VCHSRobots/TalonBreakoutV2/doc/IMG_9758.jpg

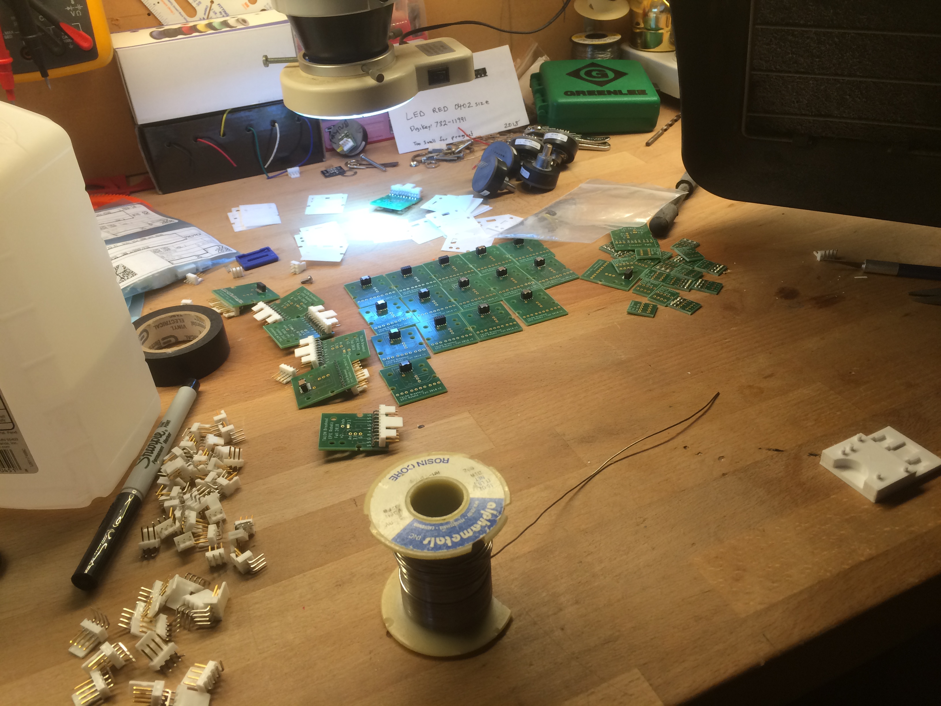
doc/IMG_9758.jpg
