VCHSRobots/TalonBreakoutV2/doc/IMG_9759.jpg

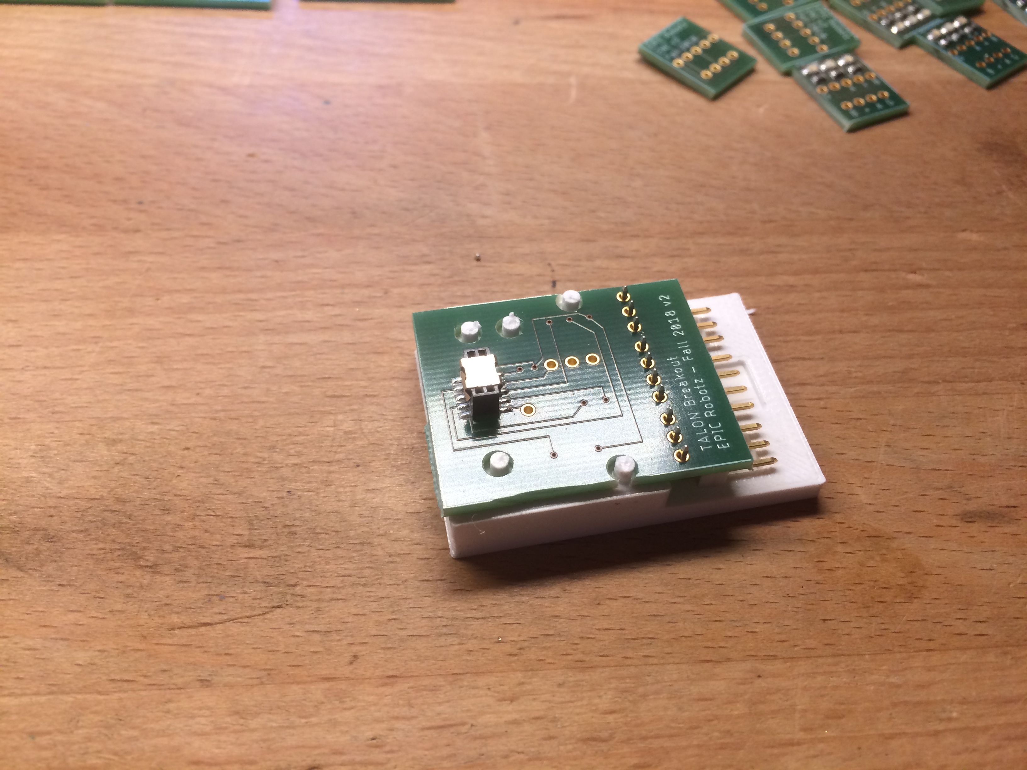
doc/IMG_9759.jpg
