VCHSRobots/TalonBreakoutV2/doc/IMG_9760.jpg

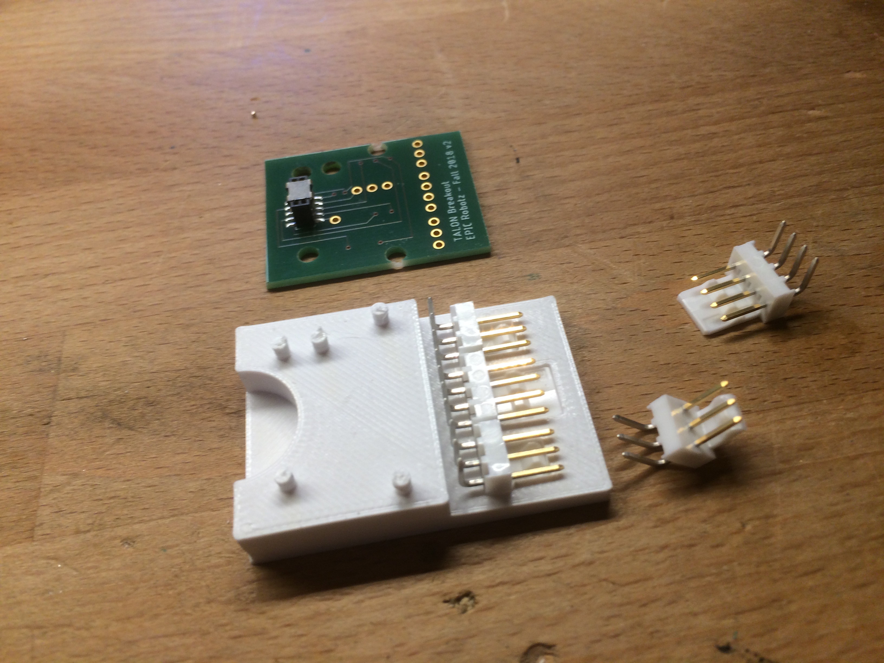
doc/IMG_9760.jpg
