VCHSRobots/TalonBreakoutV2/doc/IMG_9761.jpg

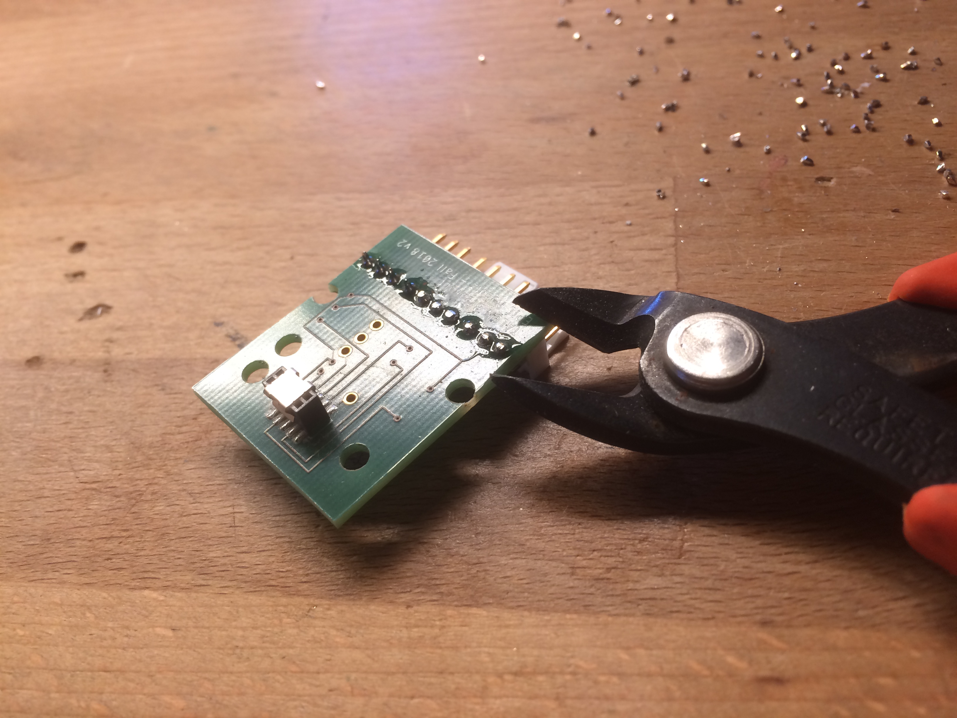
doc/IMG_9761.jpg
