VCHSRobots/TalonBreakoutV2/doc/IMG_9762.jpg

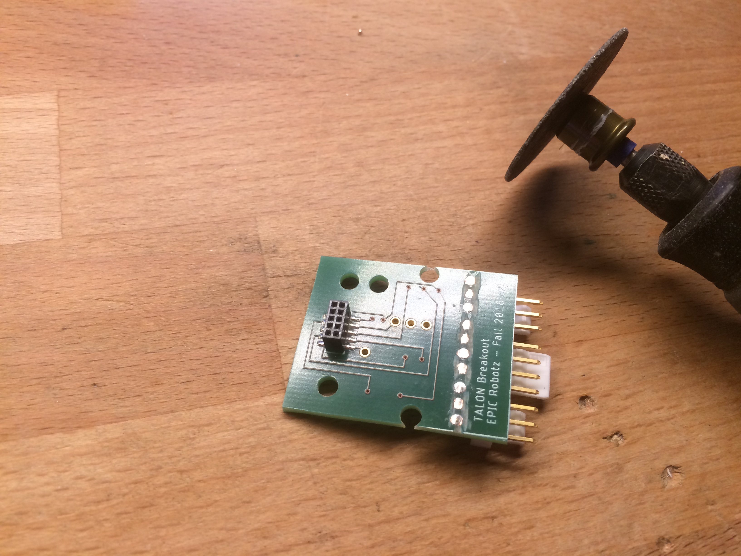
doc/IMG_9762.jpg
