VCHSRobots/TalonBreakoutV2/doc/IMG_9763.jpg

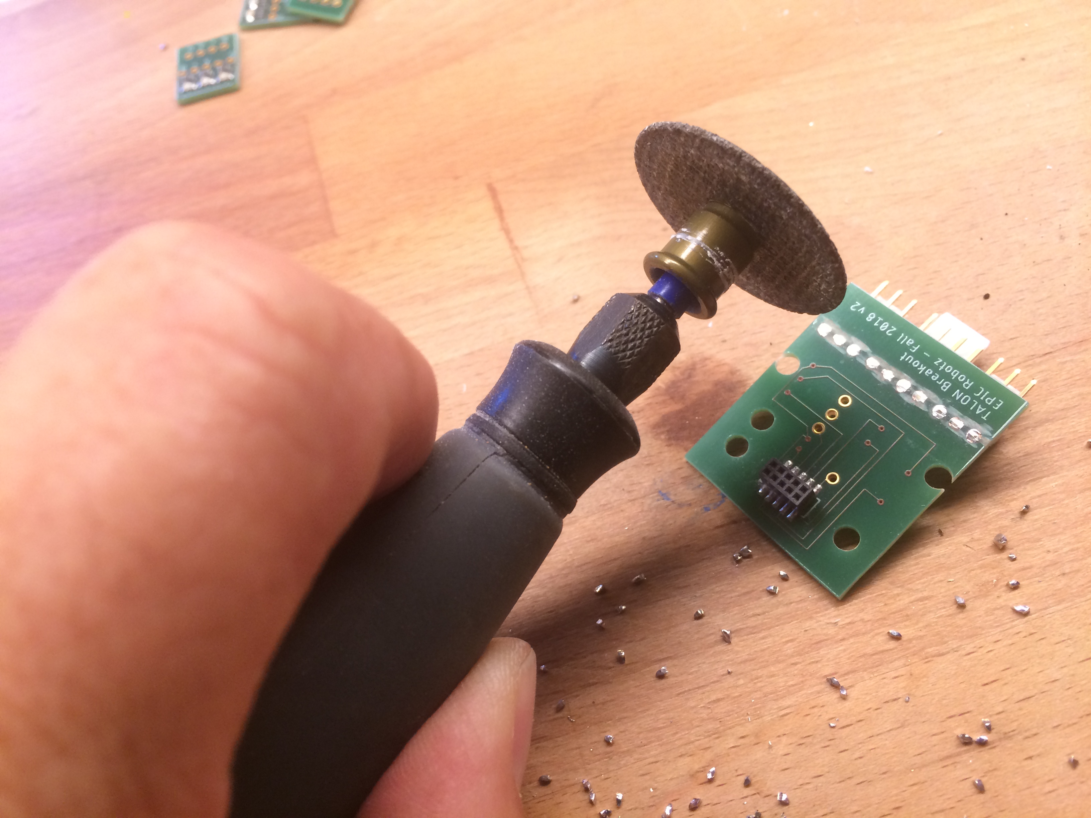
doc/IMG_9763.jpg
