VCHSRobots/TalonBreakoutV2/doc/IMG_9764.jpg

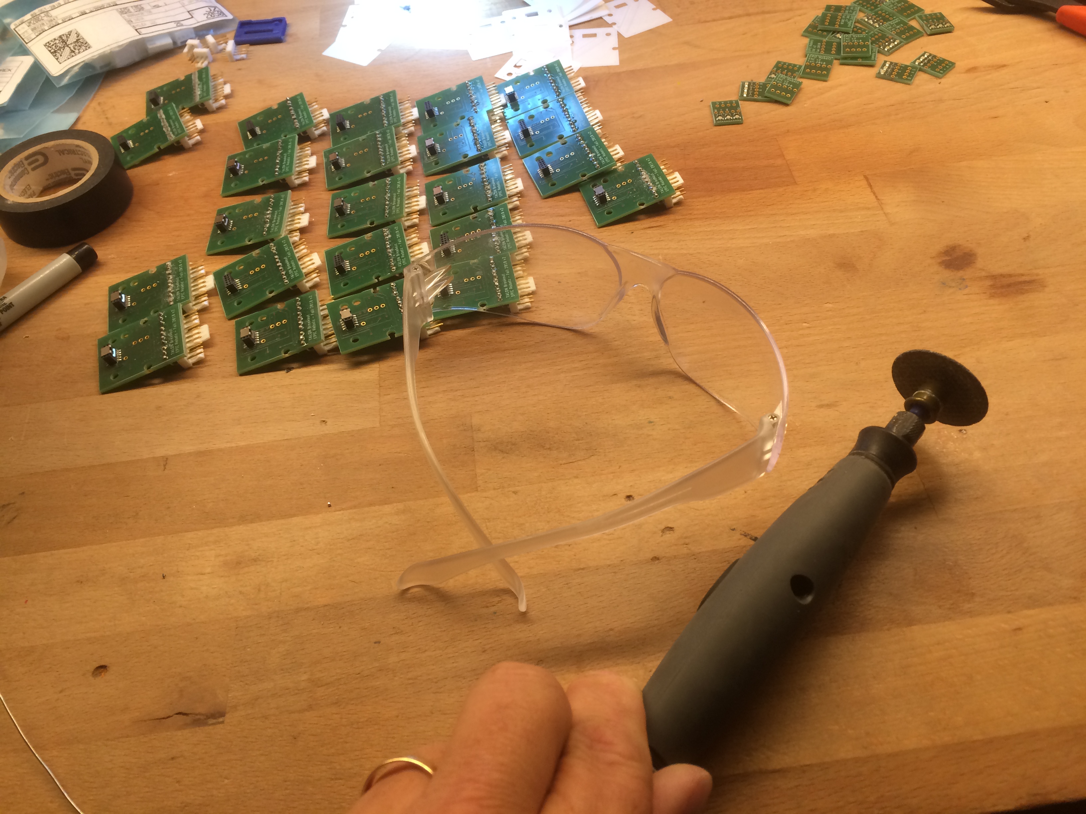
doc/IMG_9764.jpg
