VCHSRobots/TalonBreakoutV2/doc/IMG_9765.jpg

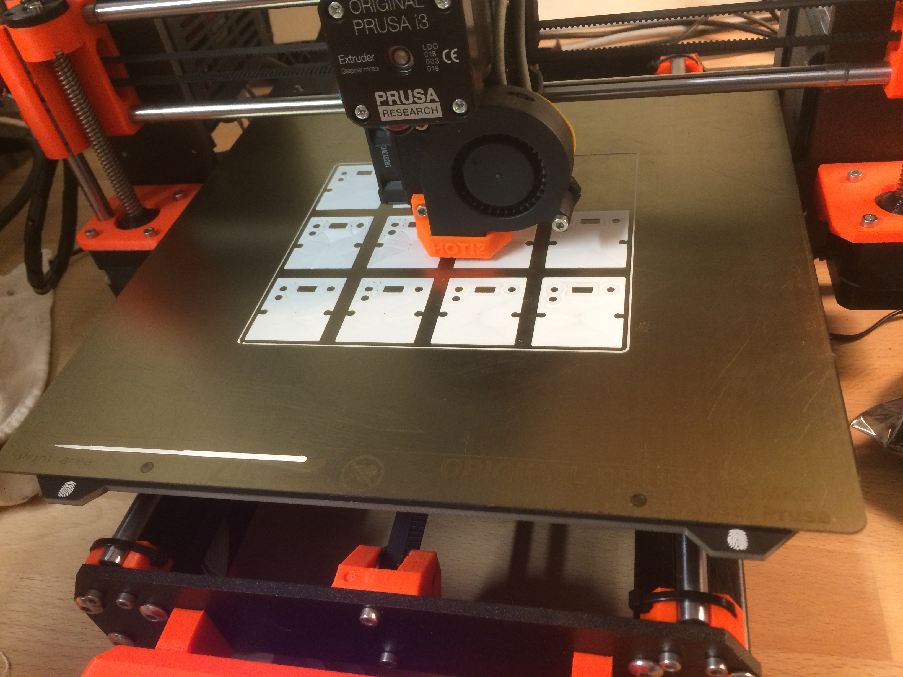
doc/IMG_9765.jpg
