VCHSRobots/TalonBreakoutV2/doc/IMG_9766.jpg

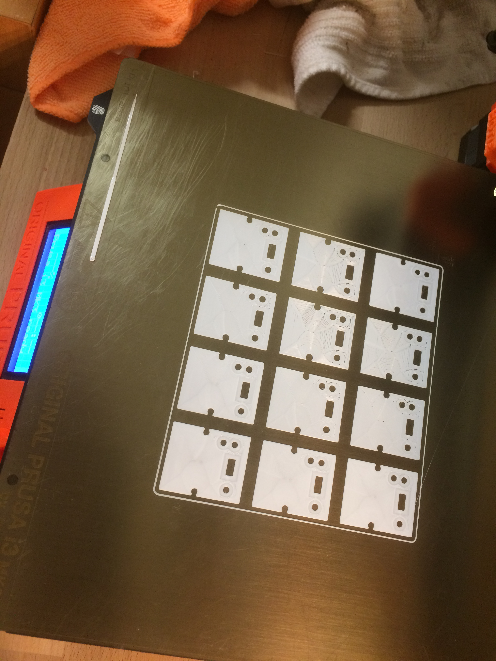
doc/IMG_9766.jpg
