VCHSRobots/TalonBreakoutV2/doc/IMG_9767.jpg

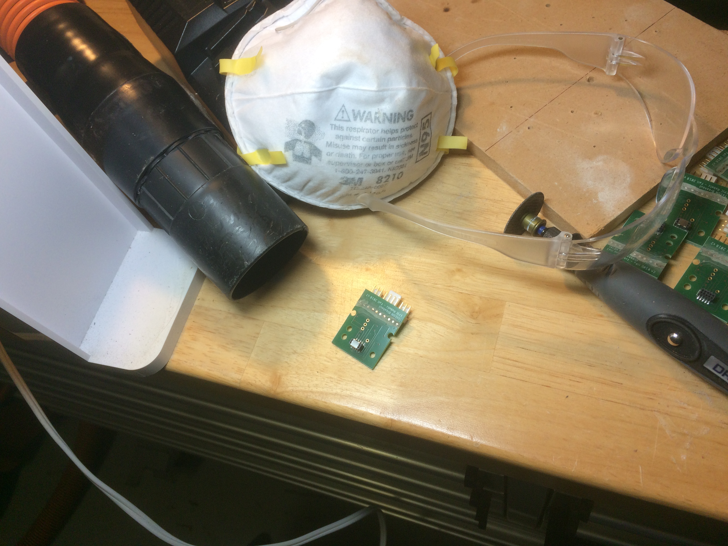
doc/IMG_9767.jpg
