VCHSRobots/TalonBreakoutV2/doc/IMG_9768.jpg

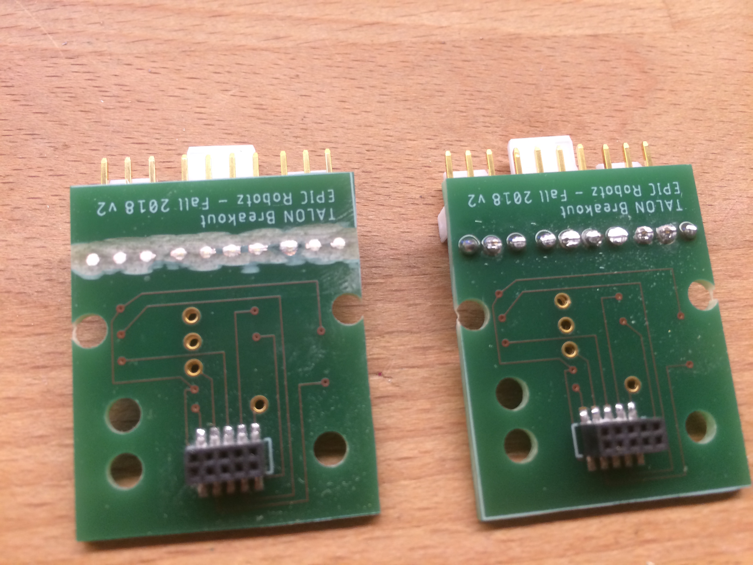
doc/IMG_9768.jpg
