VCHSRobots/TalonBreakoutV2/doc/IMG_9769.jpg

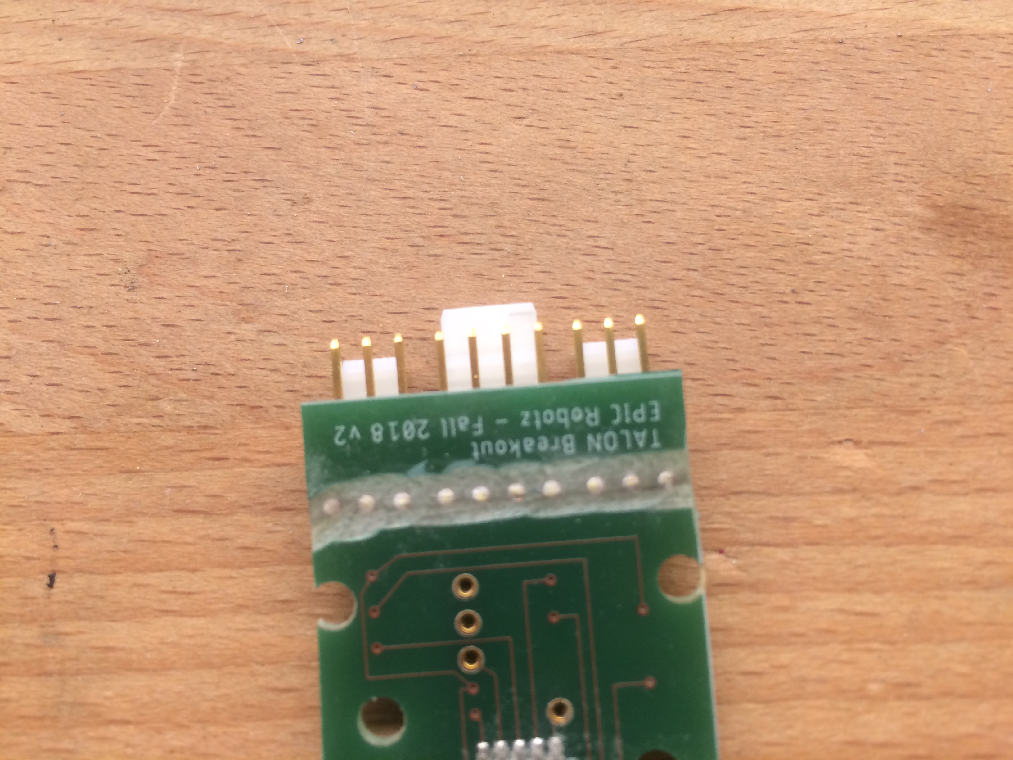
doc/IMG_9769.jpg
