VCHSRobots/TalonBreakoutV2/doc/IMG_9770.jpg

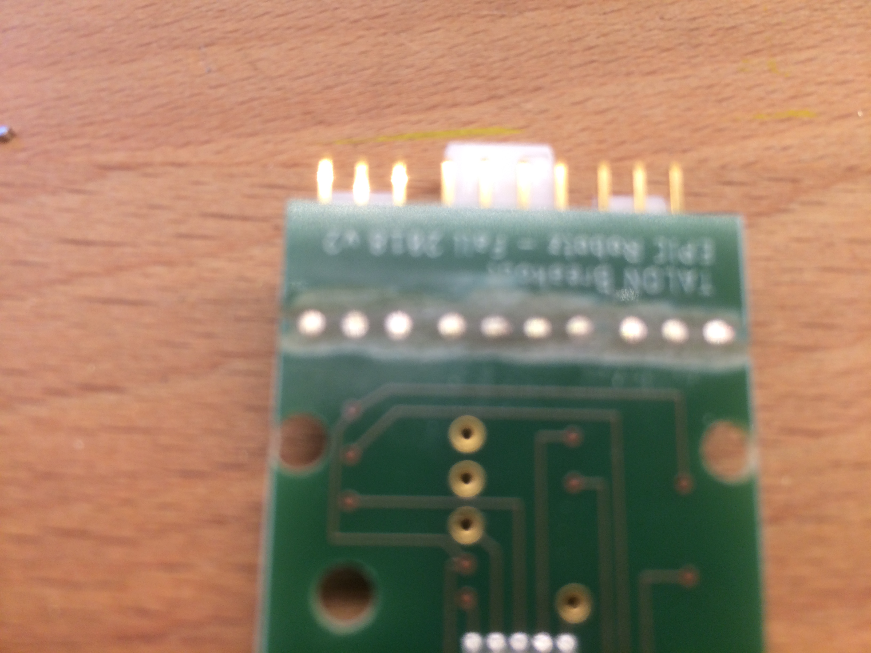
doc/IMG_9770.jpg
