VCHSRobots/TalonBreakoutV2/doc/IMG_9771.jpg

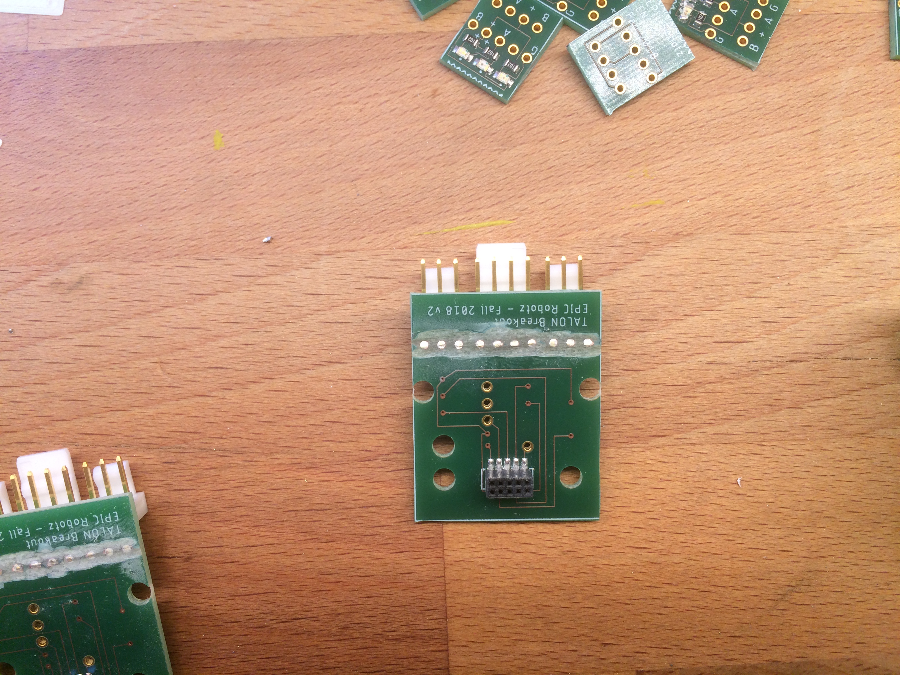
doc/IMG_9771.jpg
