VCHSRobots/TalonBreakoutV2/doc/IMG_9772.jpg

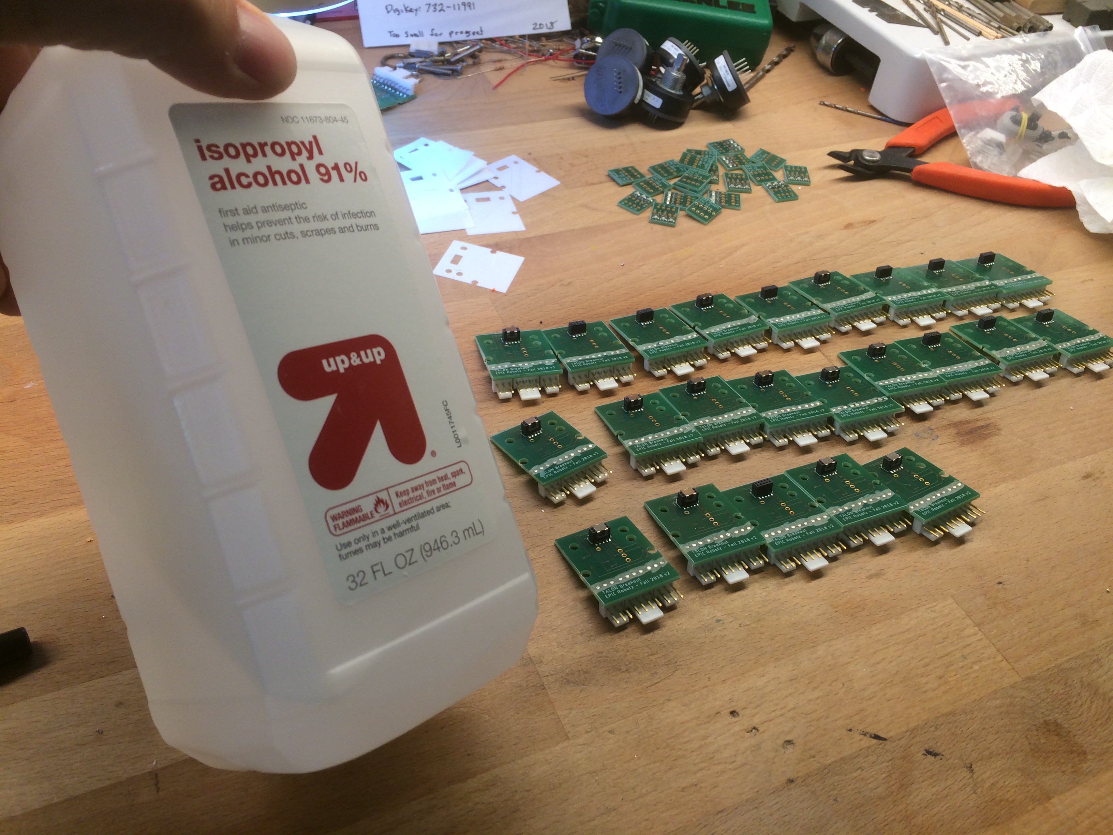
doc/IMG_9772.jpg
