VCHSRobots/TalonBreakoutV2/doc/IMG_9773.jpg

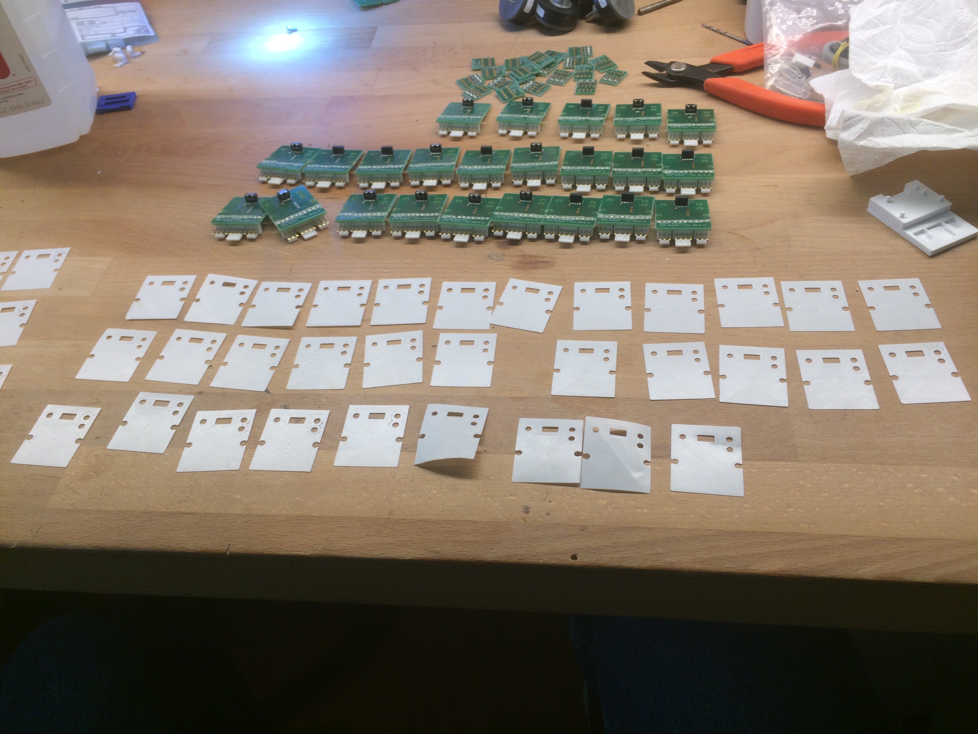
doc/IMG_9773.jpg
