VCHSRobots/TalonBreakoutV2/doc/IMG_9775.jpg

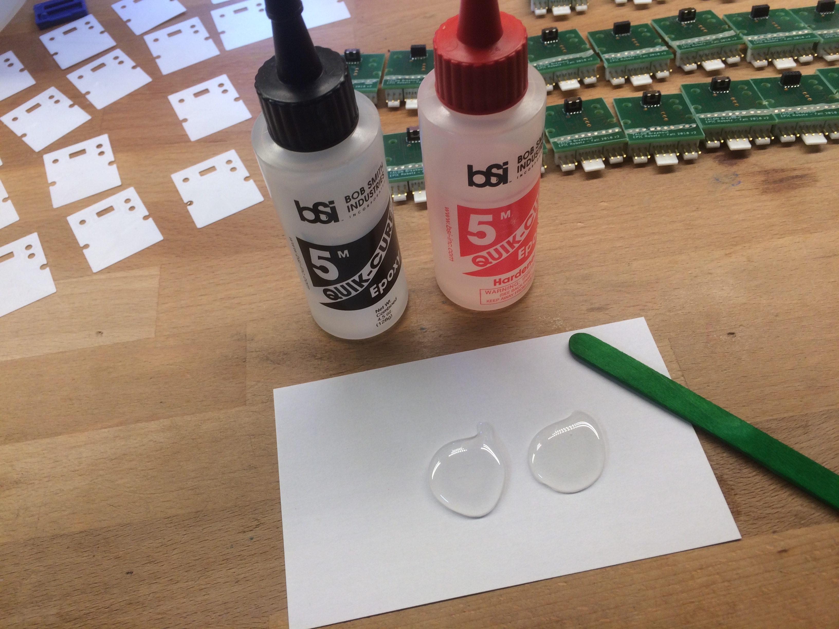
doc/IMG_9775.jpg
