VCHSRobots/TalonBreakoutV2/doc/IMG_9776.jpg

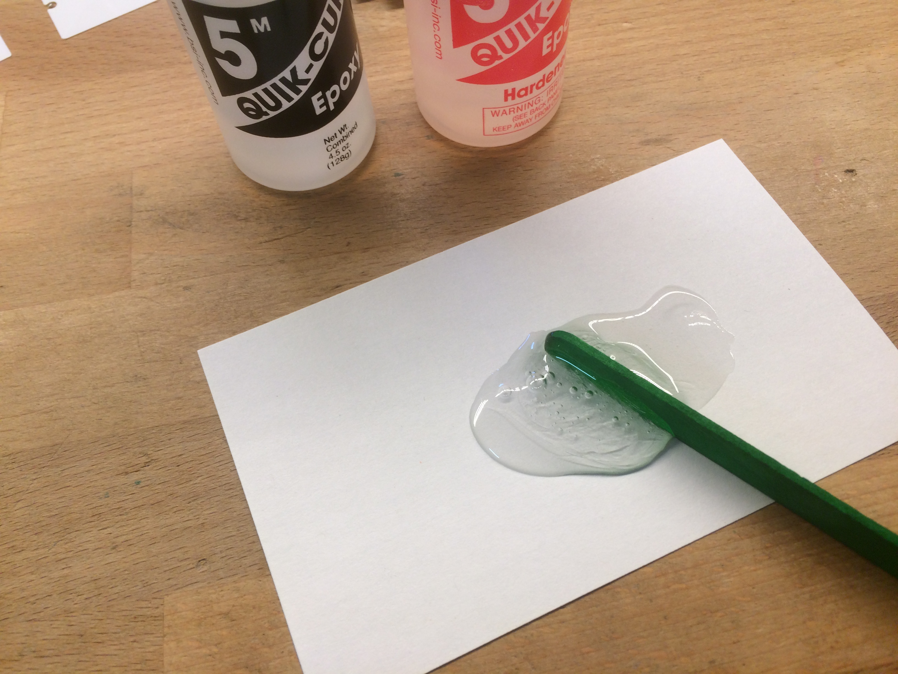
doc/IMG_9776.jpg
