VCHSRobots/TalonBreakoutV2/doc/IMG_9777.jpg

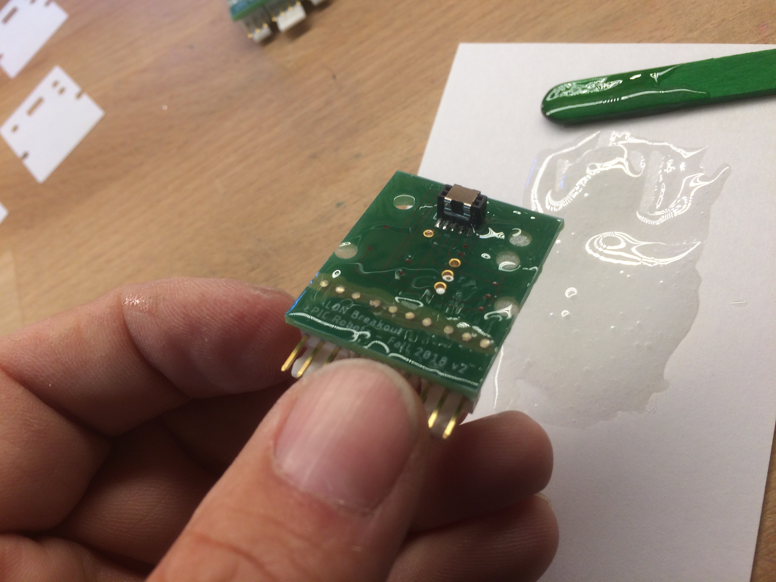
doc/IMG_9777.jpg
