VCHSRobots/TalonBreakoutV2/doc/IMG_9778.jpg

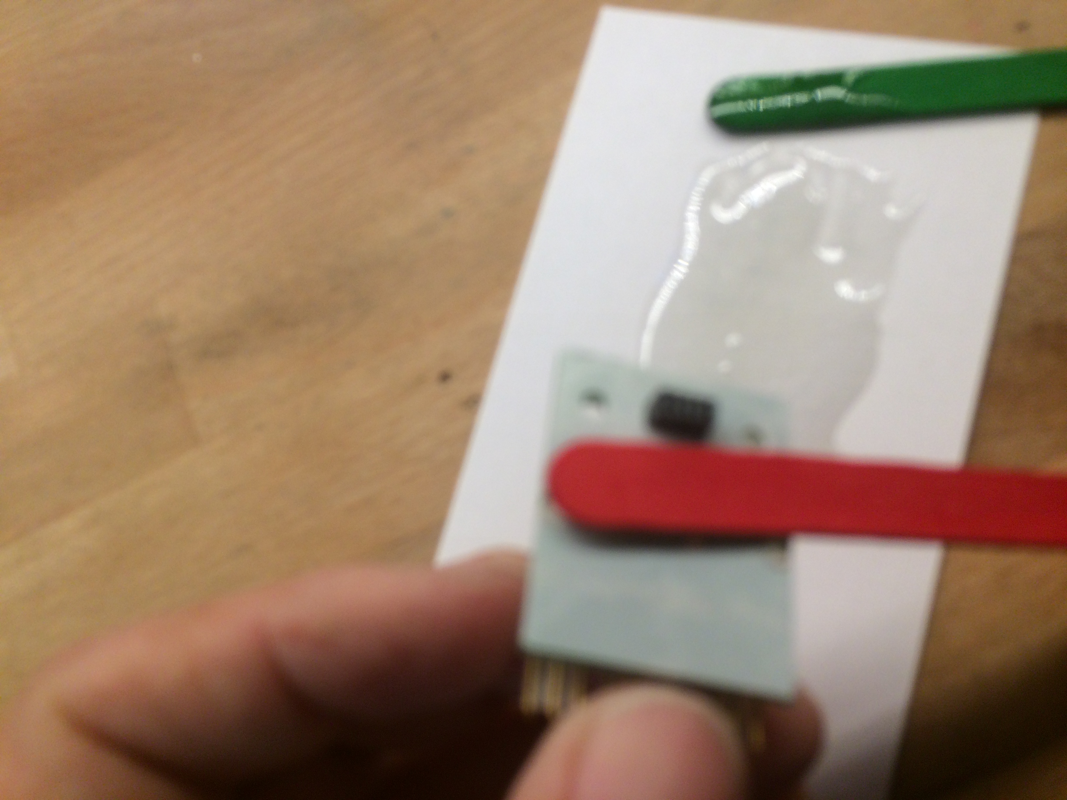
doc/IMG_9778.jpg
