VCHSRobots/TalonBreakoutV2/doc/IMG_9780.jpg

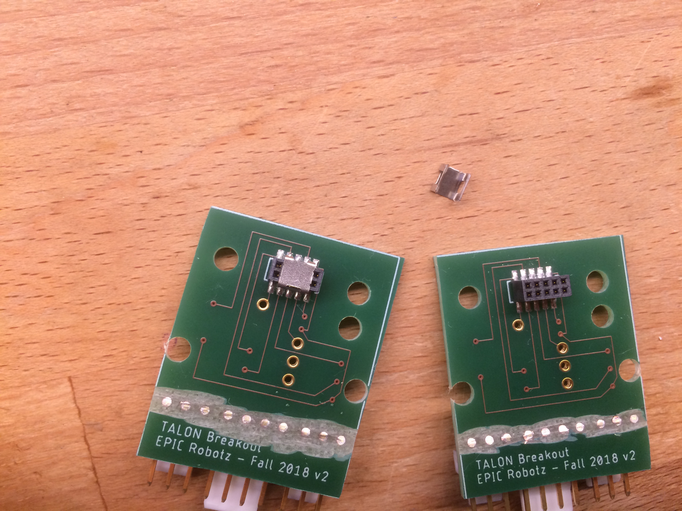
doc/IMG_9780.jpg
