VCHSRobots/TalonBreakoutV2/doc/IMG_9781.jpg

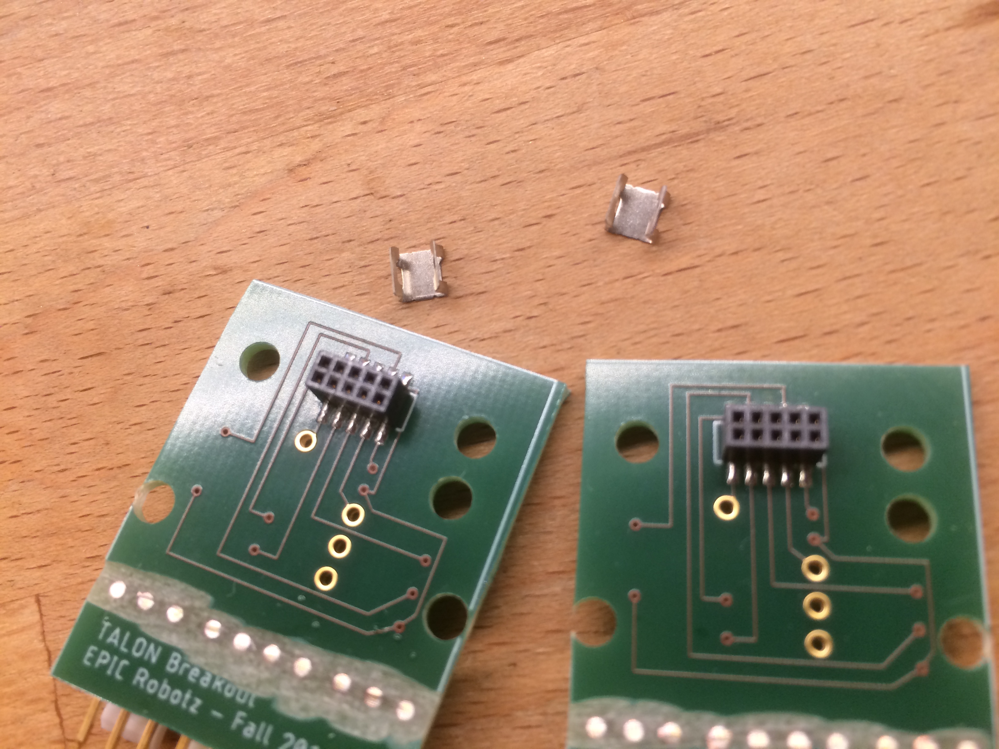
doc/IMG_9781.jpg
