VCHSRobots/TalonBreakoutV2/doc/IMG_9782.jpg

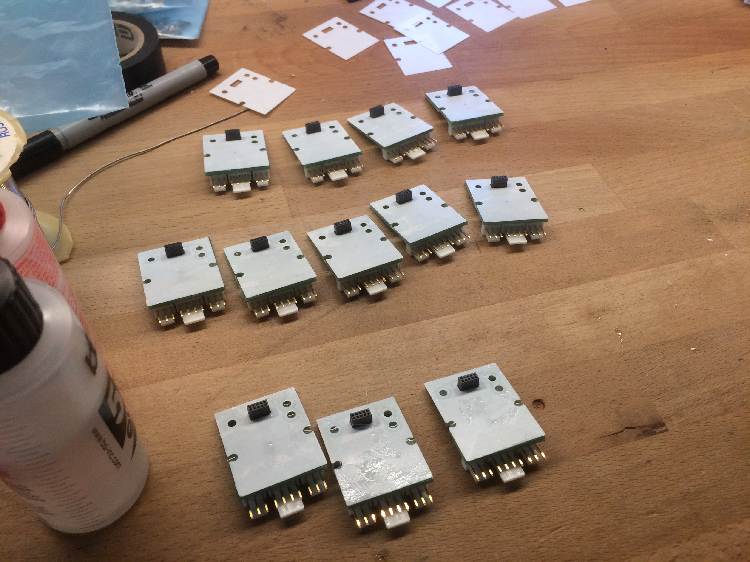
doc/IMG_9782.jpg
