VCHSRobots/TalonBreakoutV2/doc/IMG_9783.jpg

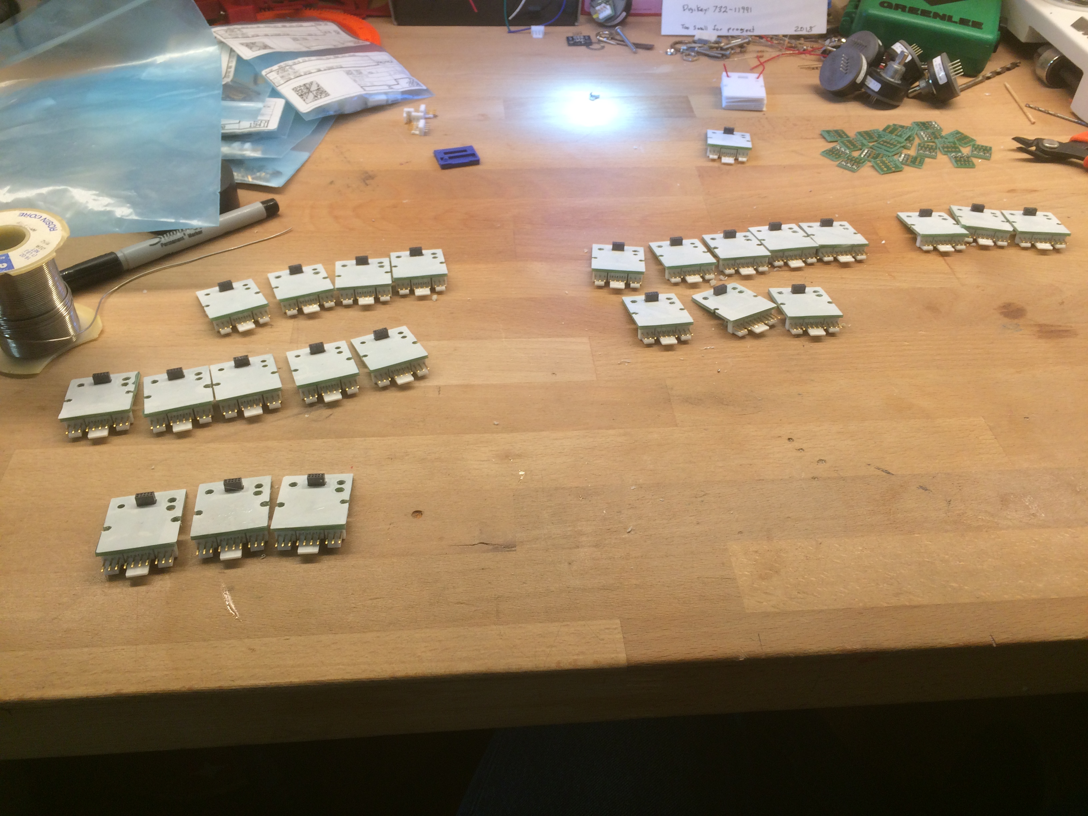
doc/IMG_9783.jpg
