VCHSRobots/TalonBreakoutV2/doc/IMG_9784.jpg

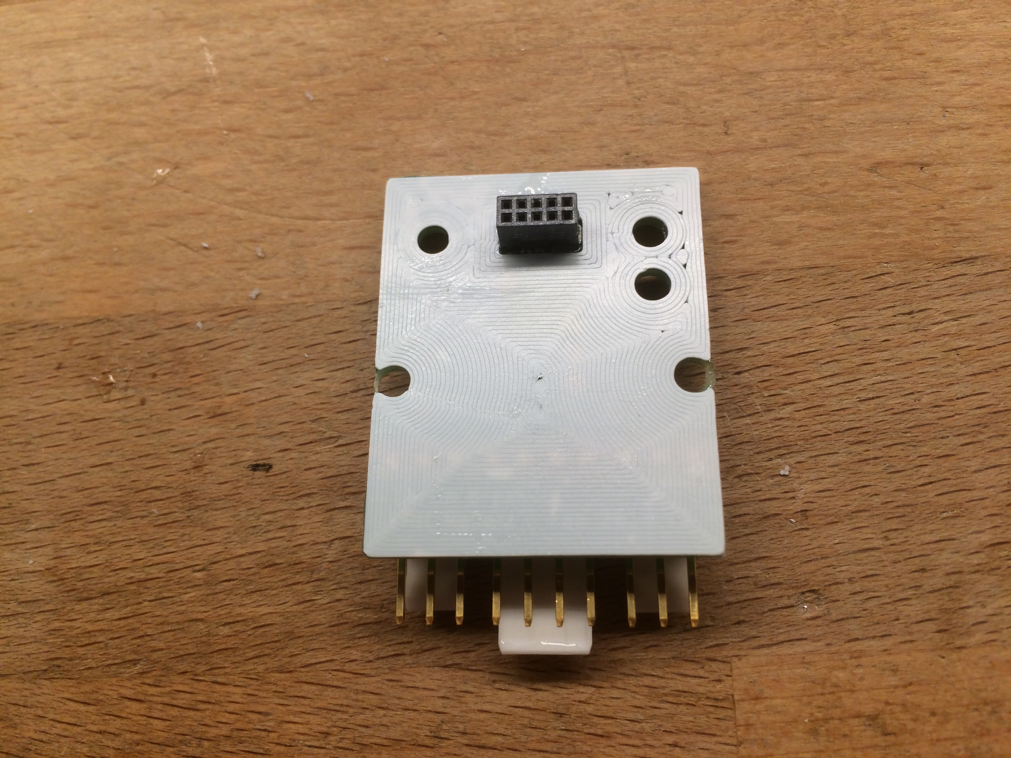
doc/IMG_9784.jpg
