VCHSRobots/TalonBreakoutV2/doc/IMG_9785.jpg

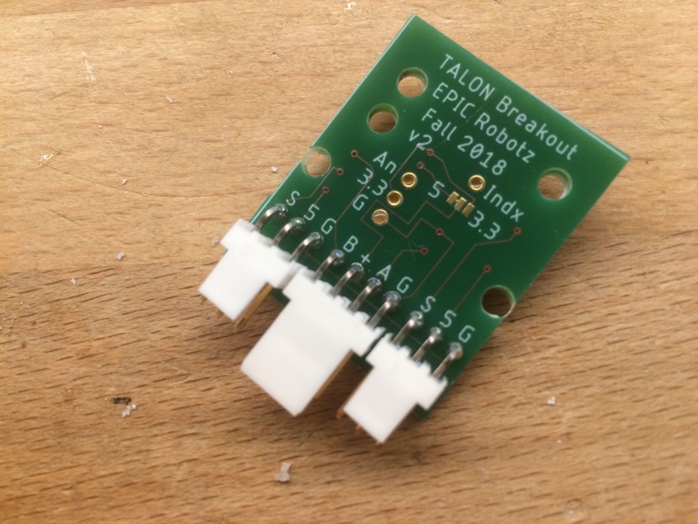
doc/IMG_9785.jpg
